AlyssonRowan/MCS-51-Computer/Hardware/(b) Core - HMC-MMB-x Main Memory Board/HMC-MMB-1 Main Memory Board (HY6264A x 4) v1.00 SCHEMATIC .pdf

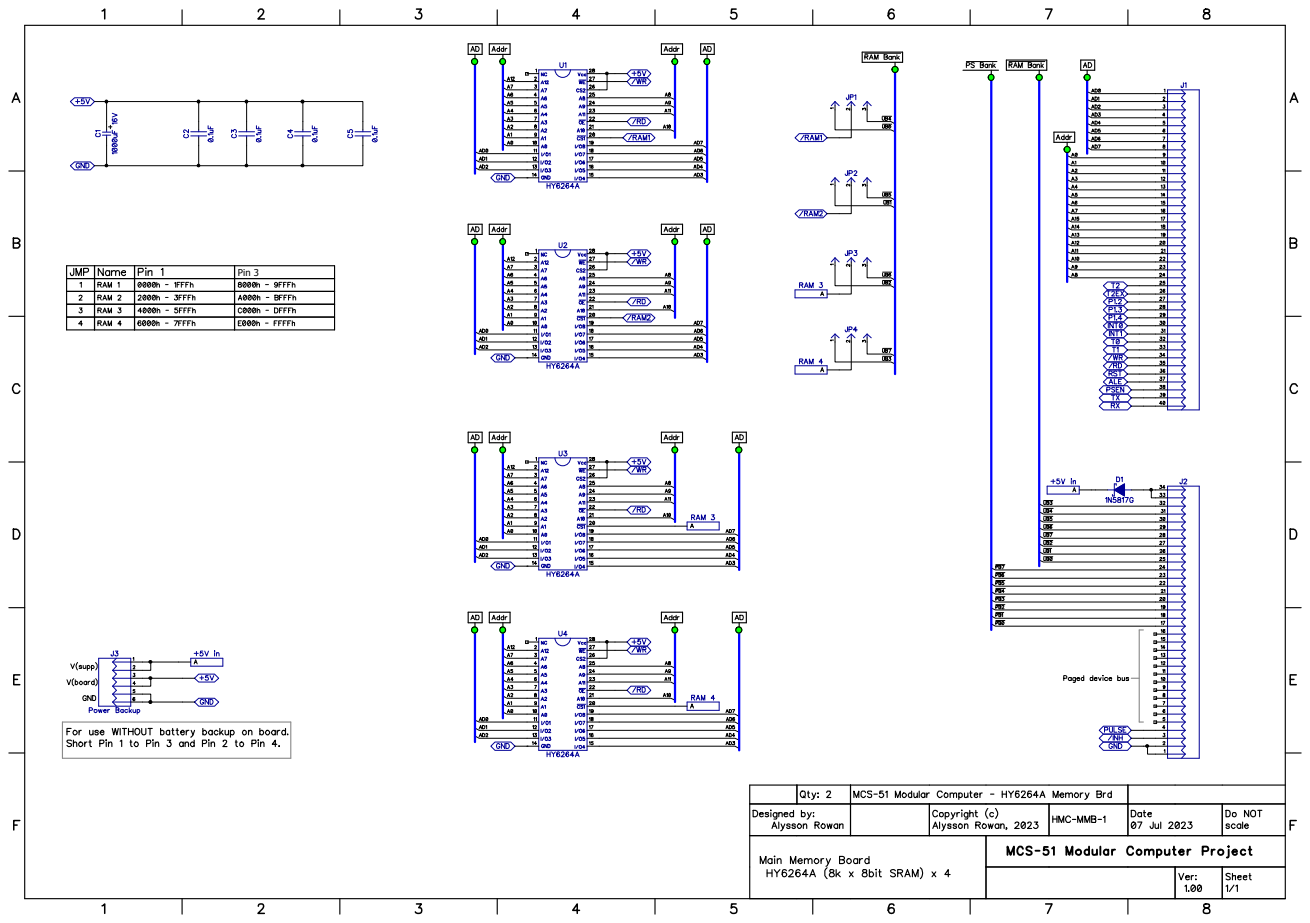
[picture p1: page 1]
Pin 3
