AlyssonRowan/MCS-51-Computer/Hardware/(b) Core - HMC-MMB-x Main Memory Board/HMC-MMB-2 Main Memory Board (configurable W24257AJ) v1.00 SCHEMATIC.pdf

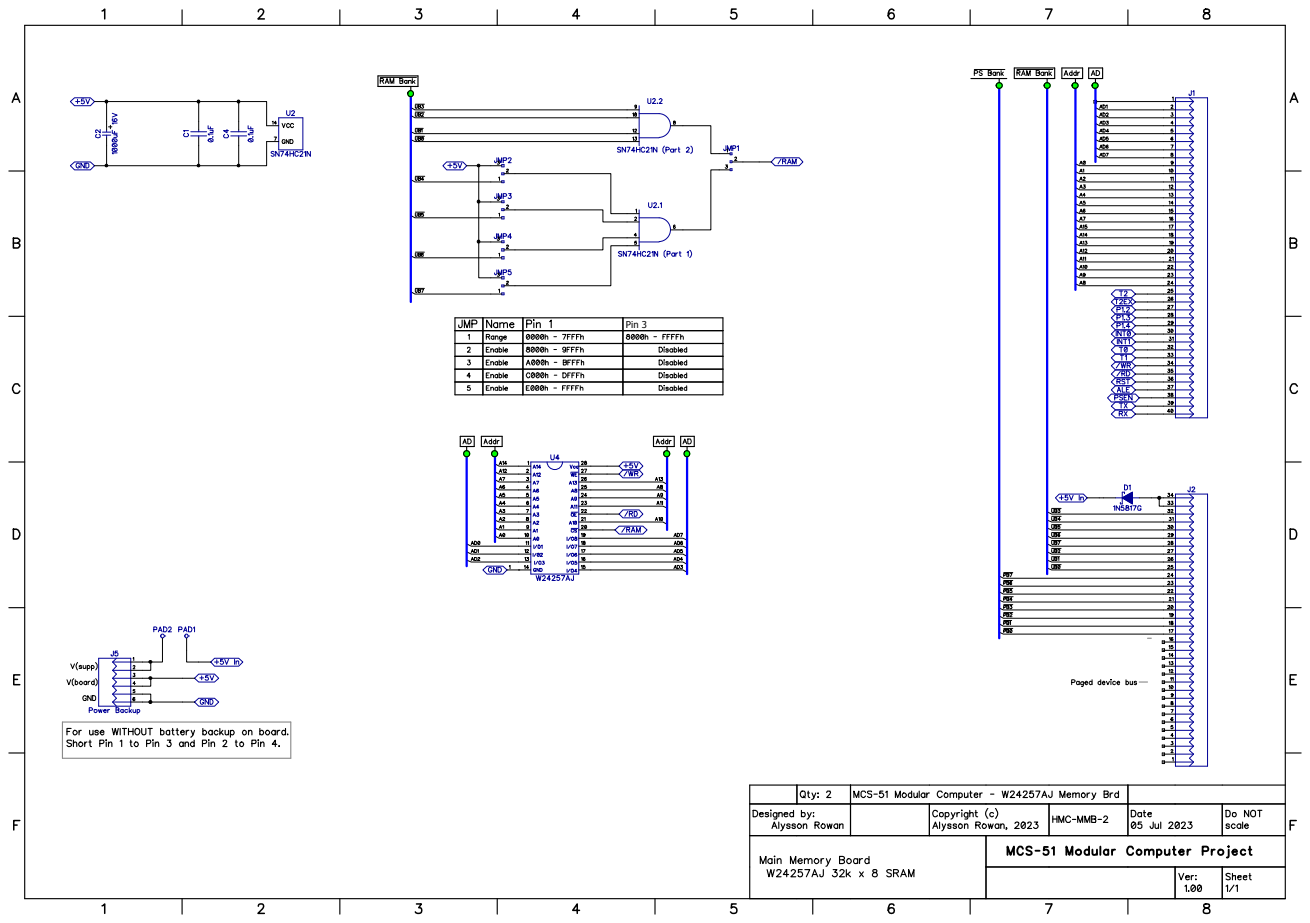
[picture p2: page 1]
Pin 3
