AlyssonRowan/MCS-51-Computer/Hardware/(b) Core - HMC-ROM-x ROM Board/HMC-ROM-1 2764, 128 ROM Board v1.00 SCHEMATIC .pdf

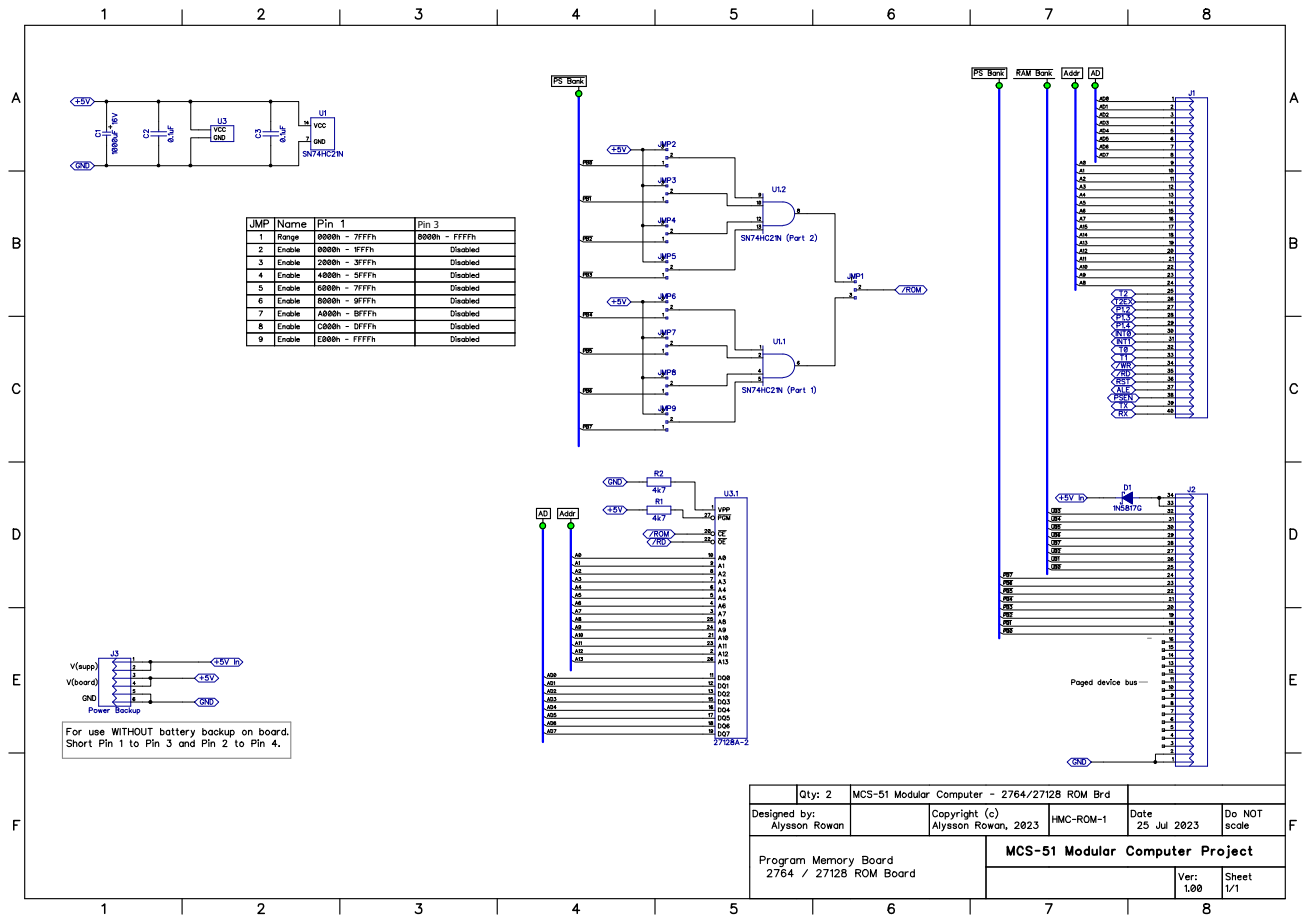
[picture p3: page 1]
Pin 3
