AlyssonRowan/MCS-51-Computer/Hardware/(b) Core - HMC-DCB-x  Daisy-Chain Board/HMC-DCB-2  Daisy-Chain Board (long) v2.00 TOP.pdf

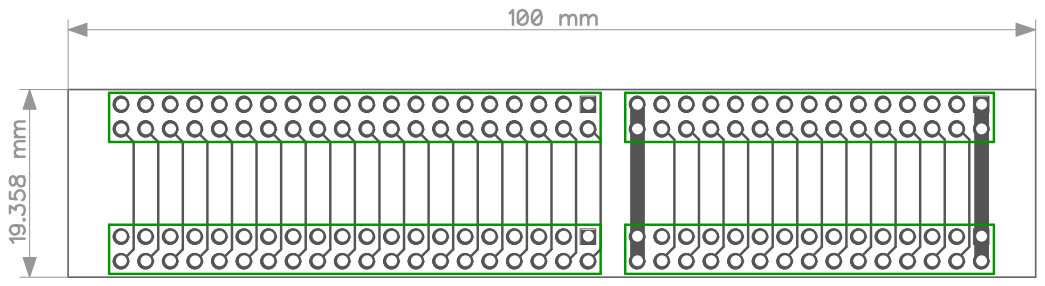
[picture p16: page 1]
