AlyssonRowan/MCS-51-Computer/Hardware/(b) Core - HMC-DCB-x  Daisy-Chain Board/HMC-DCB-2  Daisy-Chain Board (long) v2.00 X-RAY.pdf

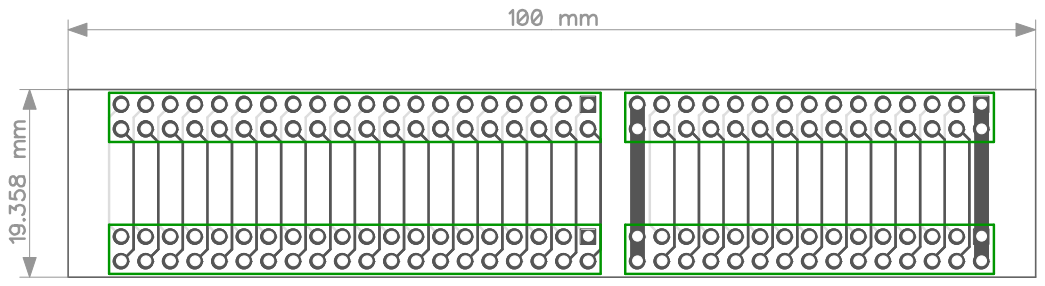
[picture p17: page 1]
