AlyssonRowan/MCS-51-Computer/Hardware/(b) Core - HMC-IB-x  Integrated Backplane/HMC-IB-1  Integrated Backplane MOBO v1.65 BOTTOM.pdf

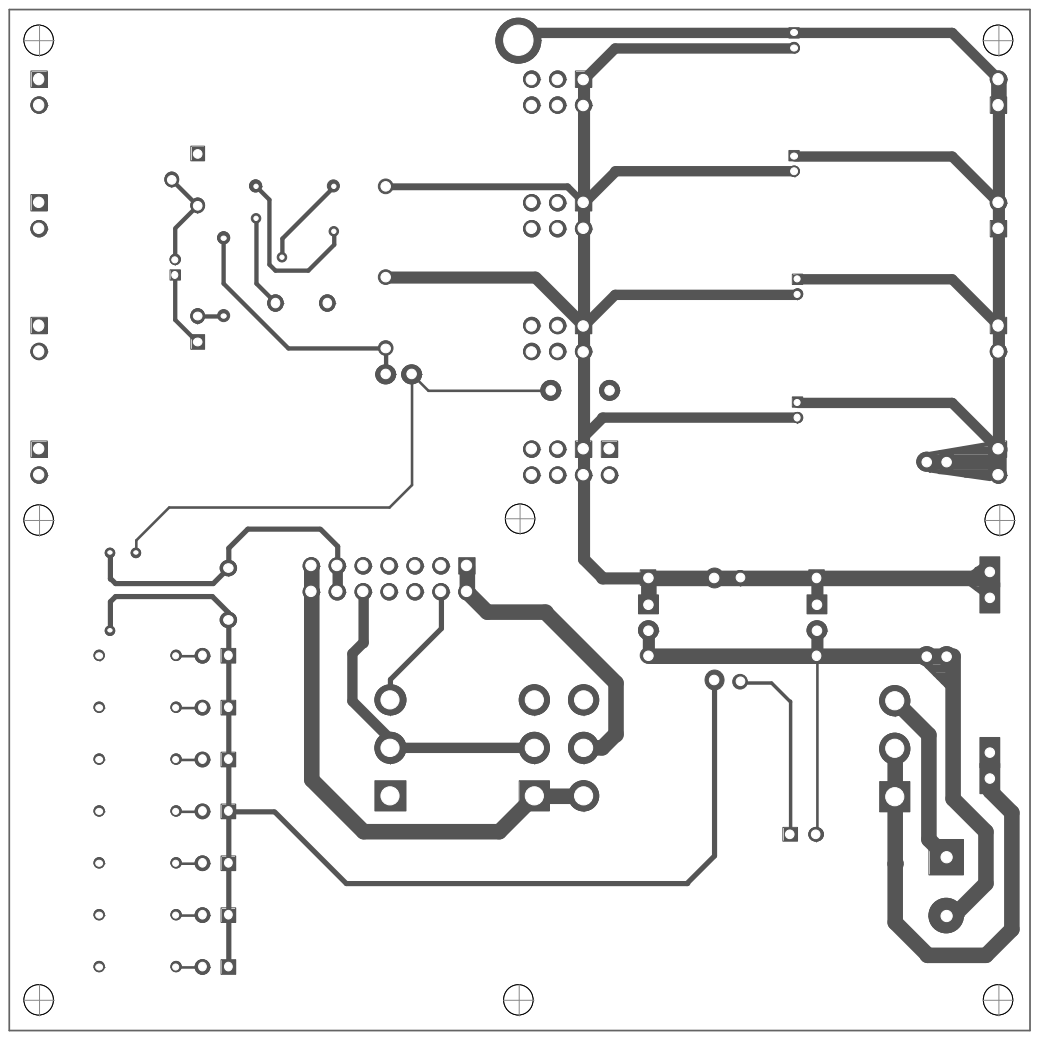
[picture p18: page 1]
