AlyssonRowan/MCS-51-Computer/Hardware/(b) Core - HMC-IB-x  Integrated Backplane/HMC-IB-2  Integrated Backplane BUS daughterboard v1.10 TOP.pdf

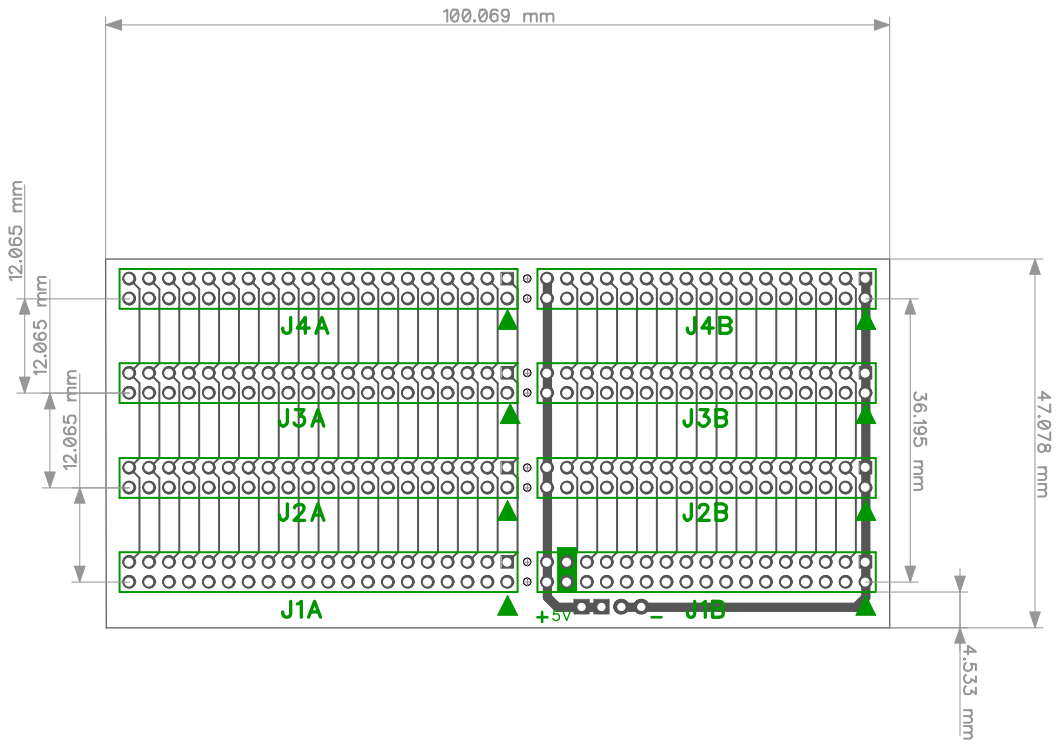
[picture p22: page 1]
