AlyssonRowan/MCS-51-Computer/Hardware/(b) Core - HMC-MB-x  Modular Backplane/HMC-MB-1  Modular Backplane A - 40p v2.00 TOP.pdf

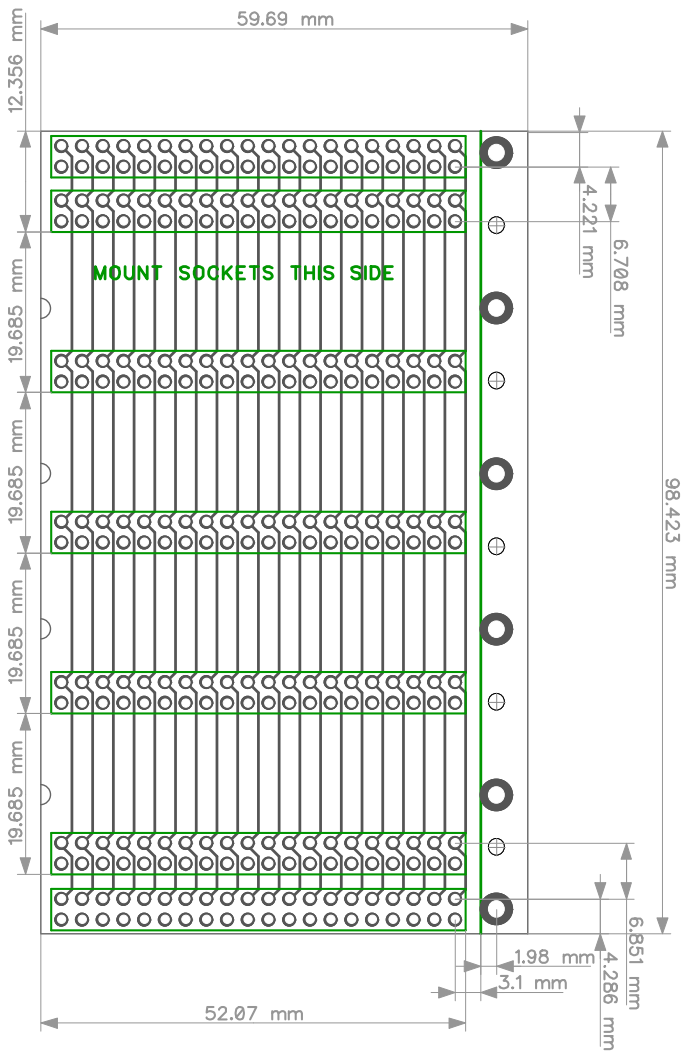
[picture p25: page 1]
