AlyssonRowan/MCS-51-Computer/Hardware/(b) Core - HMC-MB-x  Modular Backplane/HMC-MB-1  Modular Backplane A - 40p v2.00 X-RAY.pdf

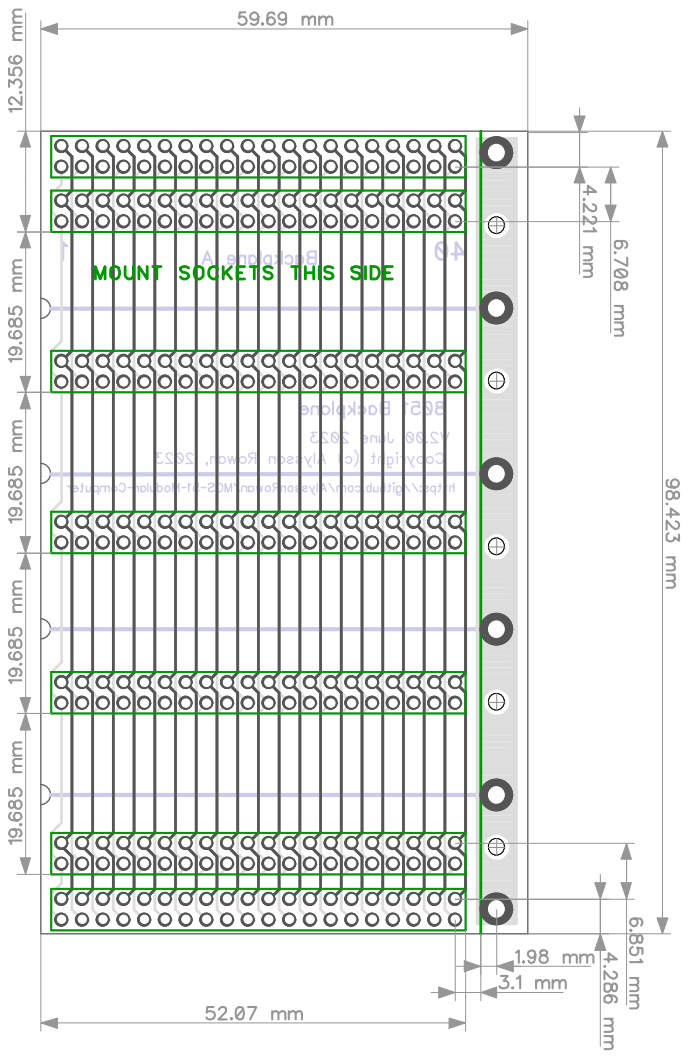
[picture p26: page 1]
