AlyssonRowan/MCS-51-Computer/Hardware/(b) Core - HMC-MB-x  Modular Backplane/HMC-MB-2  Modular Backplane B - 34p v2.00 TOP.pdf

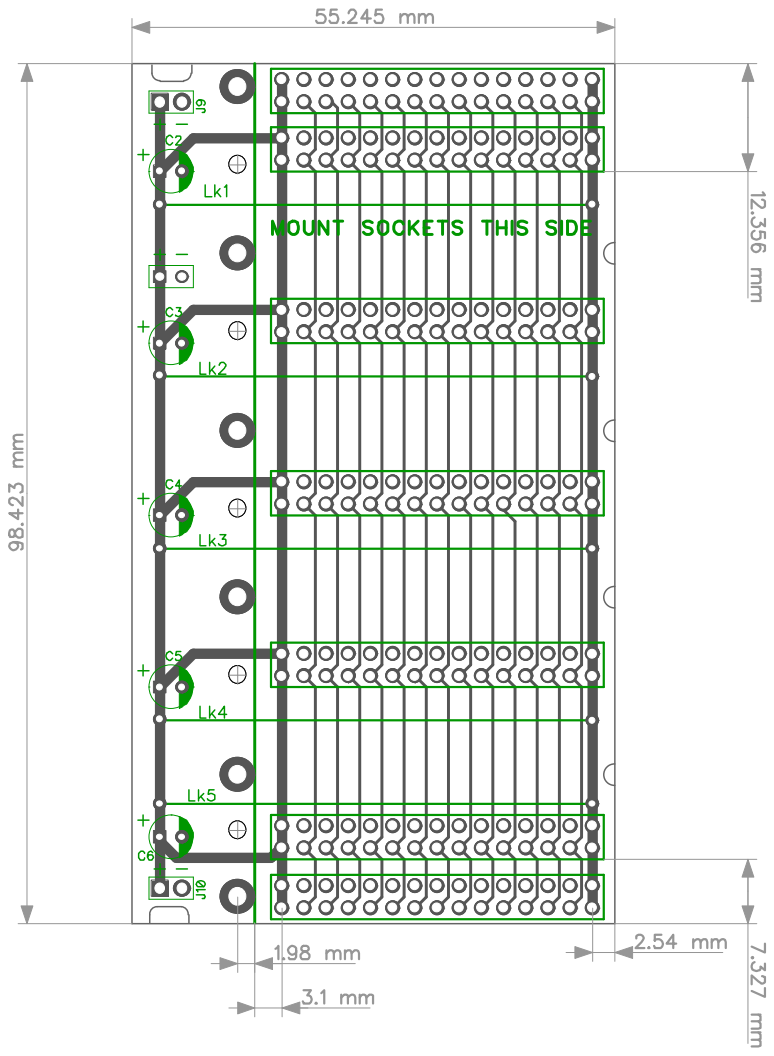
[picture p28: page 1]
