AlyssonRowan/MCS-51-Computer/Hardware/(b) Core - HMC-MB-x  Modular Backplane/HMC-MB-2  Modular Backplane B - 34p v2.00 X-RAY.pdf

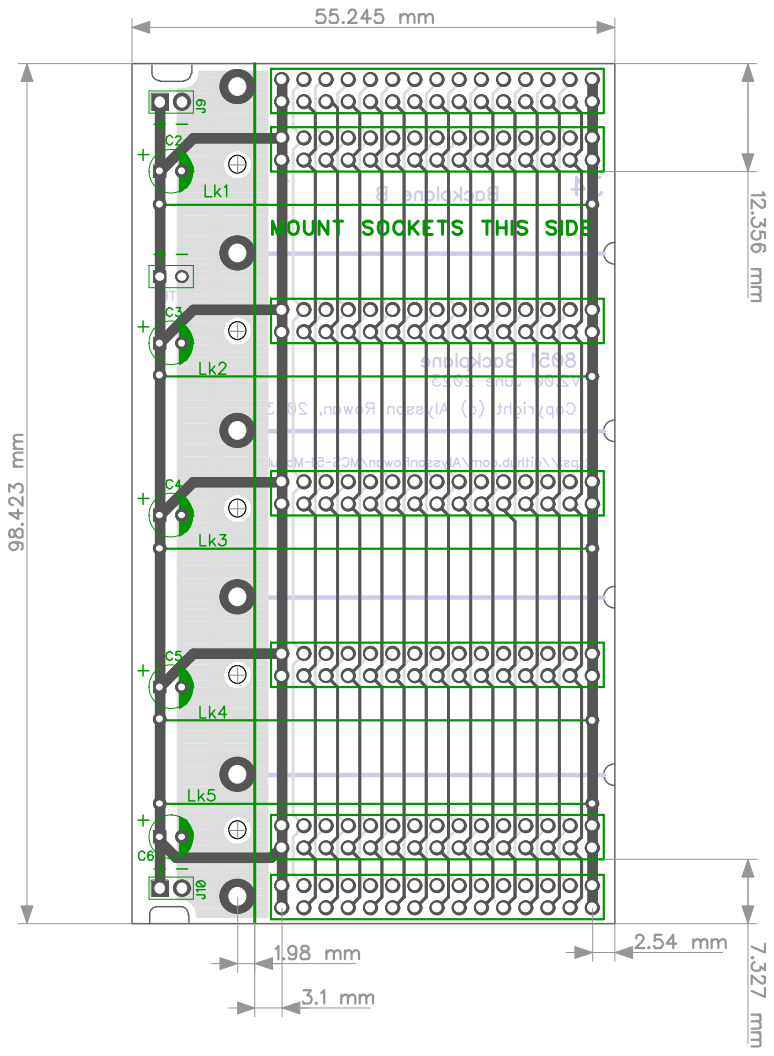
[picture p29: page 1]
