AlyssonRowan/MCS-51-Computer/Hardware/(b) Core - HMC-MMB-x Main Memory Board/HMC-MMB-2 Main Memory Board (configurable W24257AJ) v1.00 BOTTOM.pdf

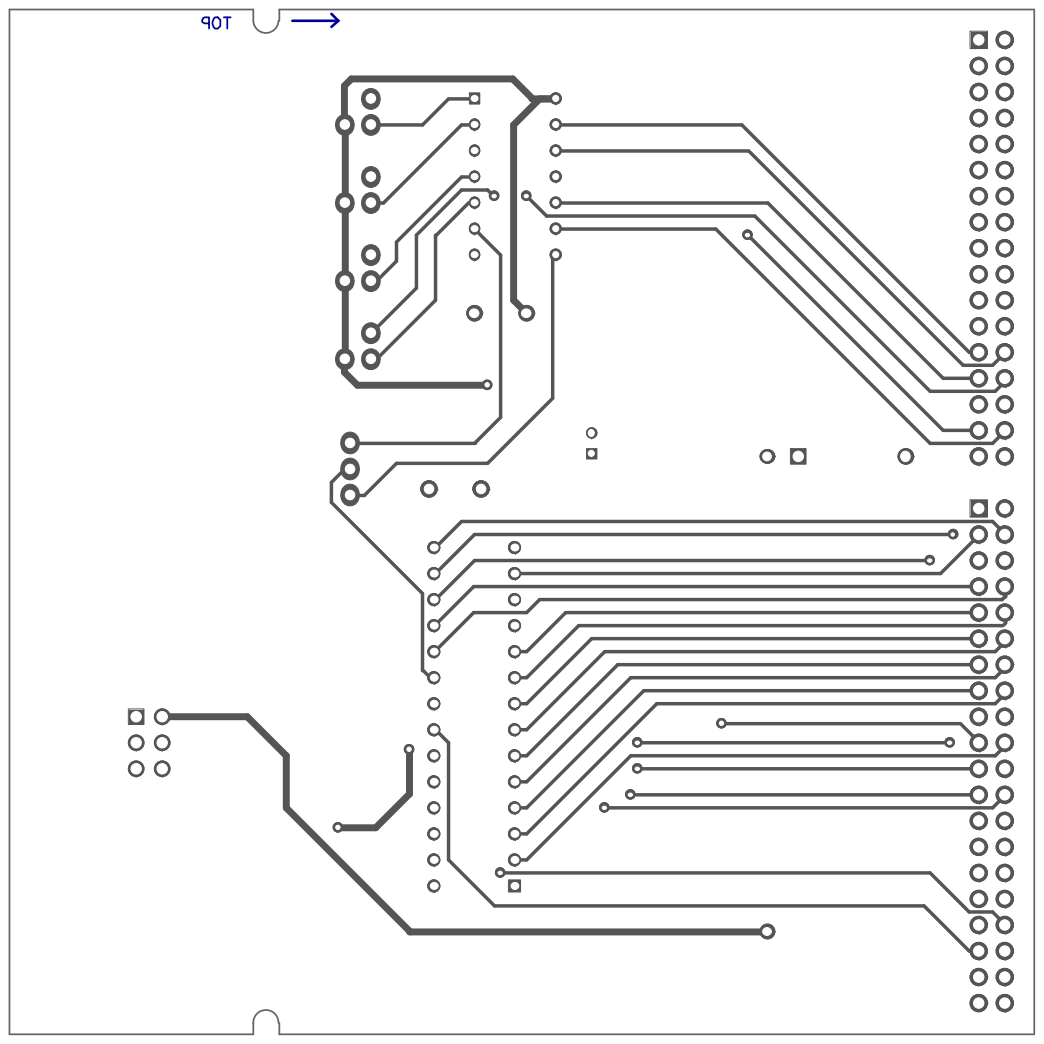
[picture p33: page 1]
