AlyssonRowan/MCS-51-Computer/Hardware/(b) Core - HMC-MMB-x Main Memory Board/HMC-MMB-2 Main Memory Board (configurable W24257AJ) v1.00 TOP.pdf

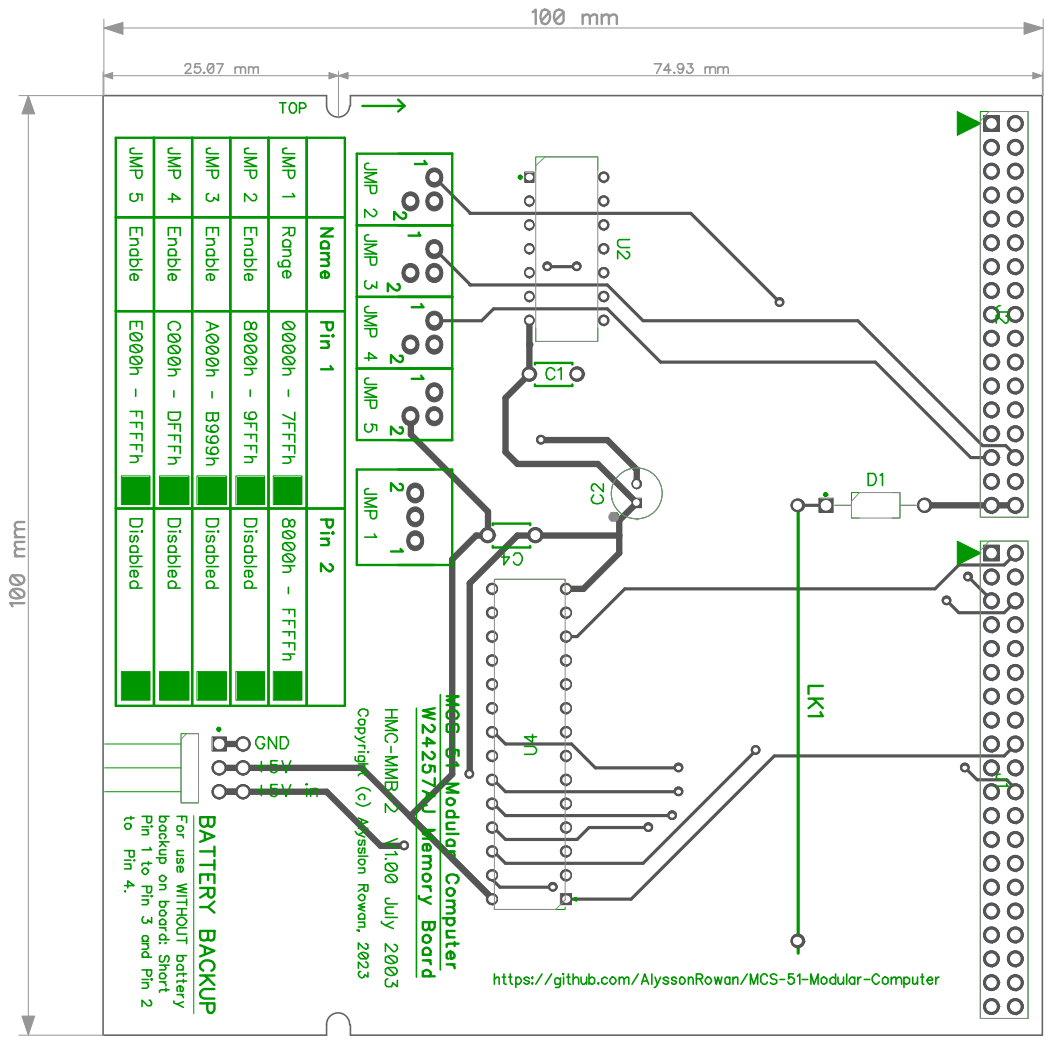
[picture p34: page 1]
