AlyssonRowan/MCS-51-Computer/Hardware/(b) Core - HMC-PB-1  ProductionBackplane/HMC-PB-1 ProductionBackplane (4 slot bus) v1.00 X-RAY.pdf

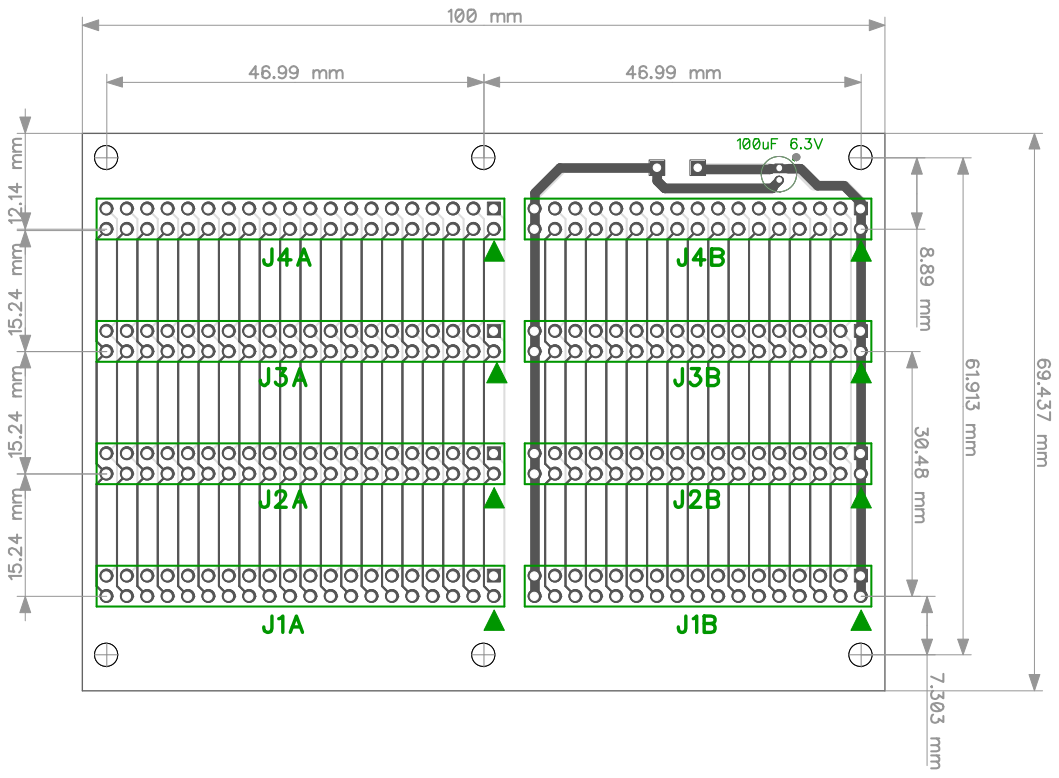
[picture p38: page 1]
