AlyssonRowan/MCS-51-Computer/Hardware/(b) Core - HMC-PR-1 Processor Board/HMC-PR-1 Processor Board v1.20 BOTTOM.pdf

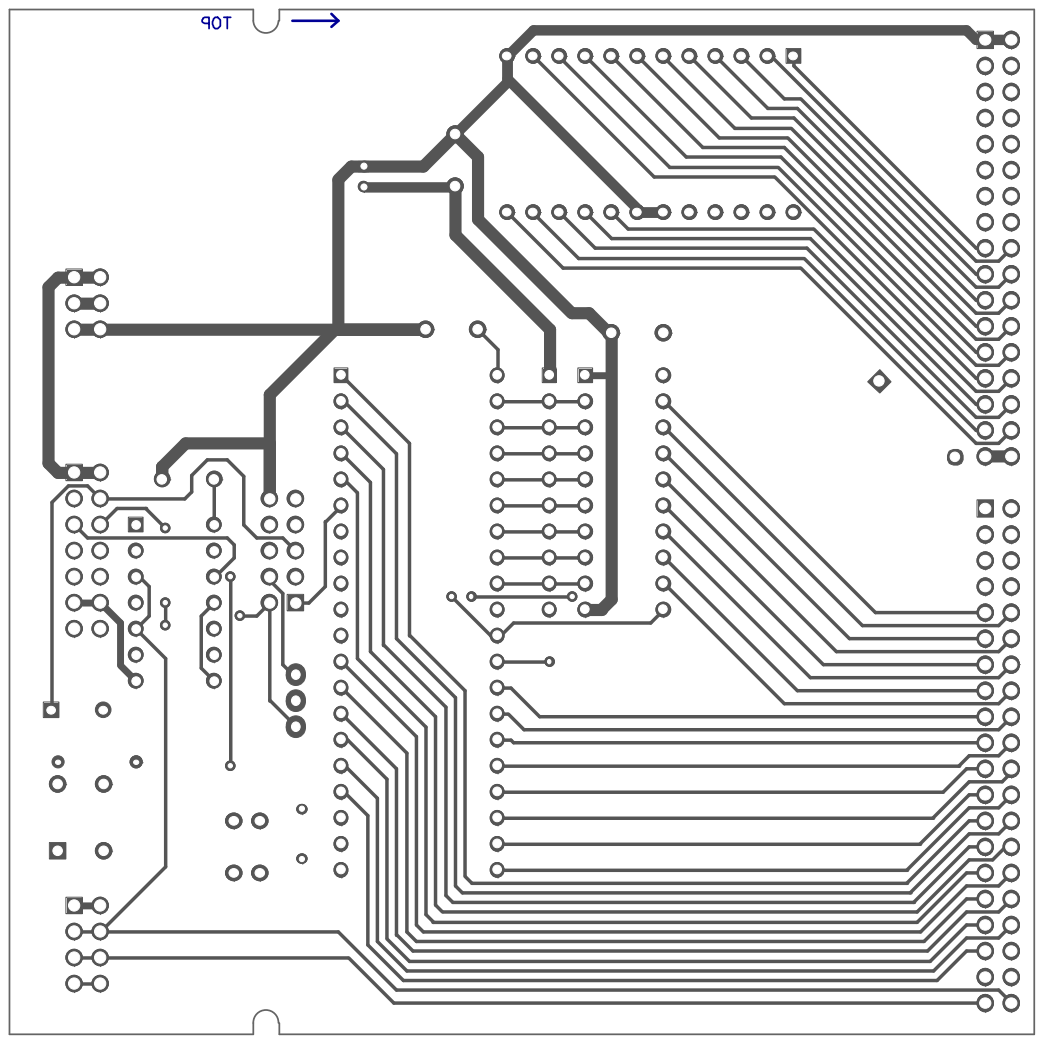
[picture p39: page 1]
