AlyssonRowan/MCS-51-Computer/Hardware/(b) Core - HMC-PR-1 Processor Board/HMC-PR-1 Processor Board v1.20 SCHEMATIC.pdf

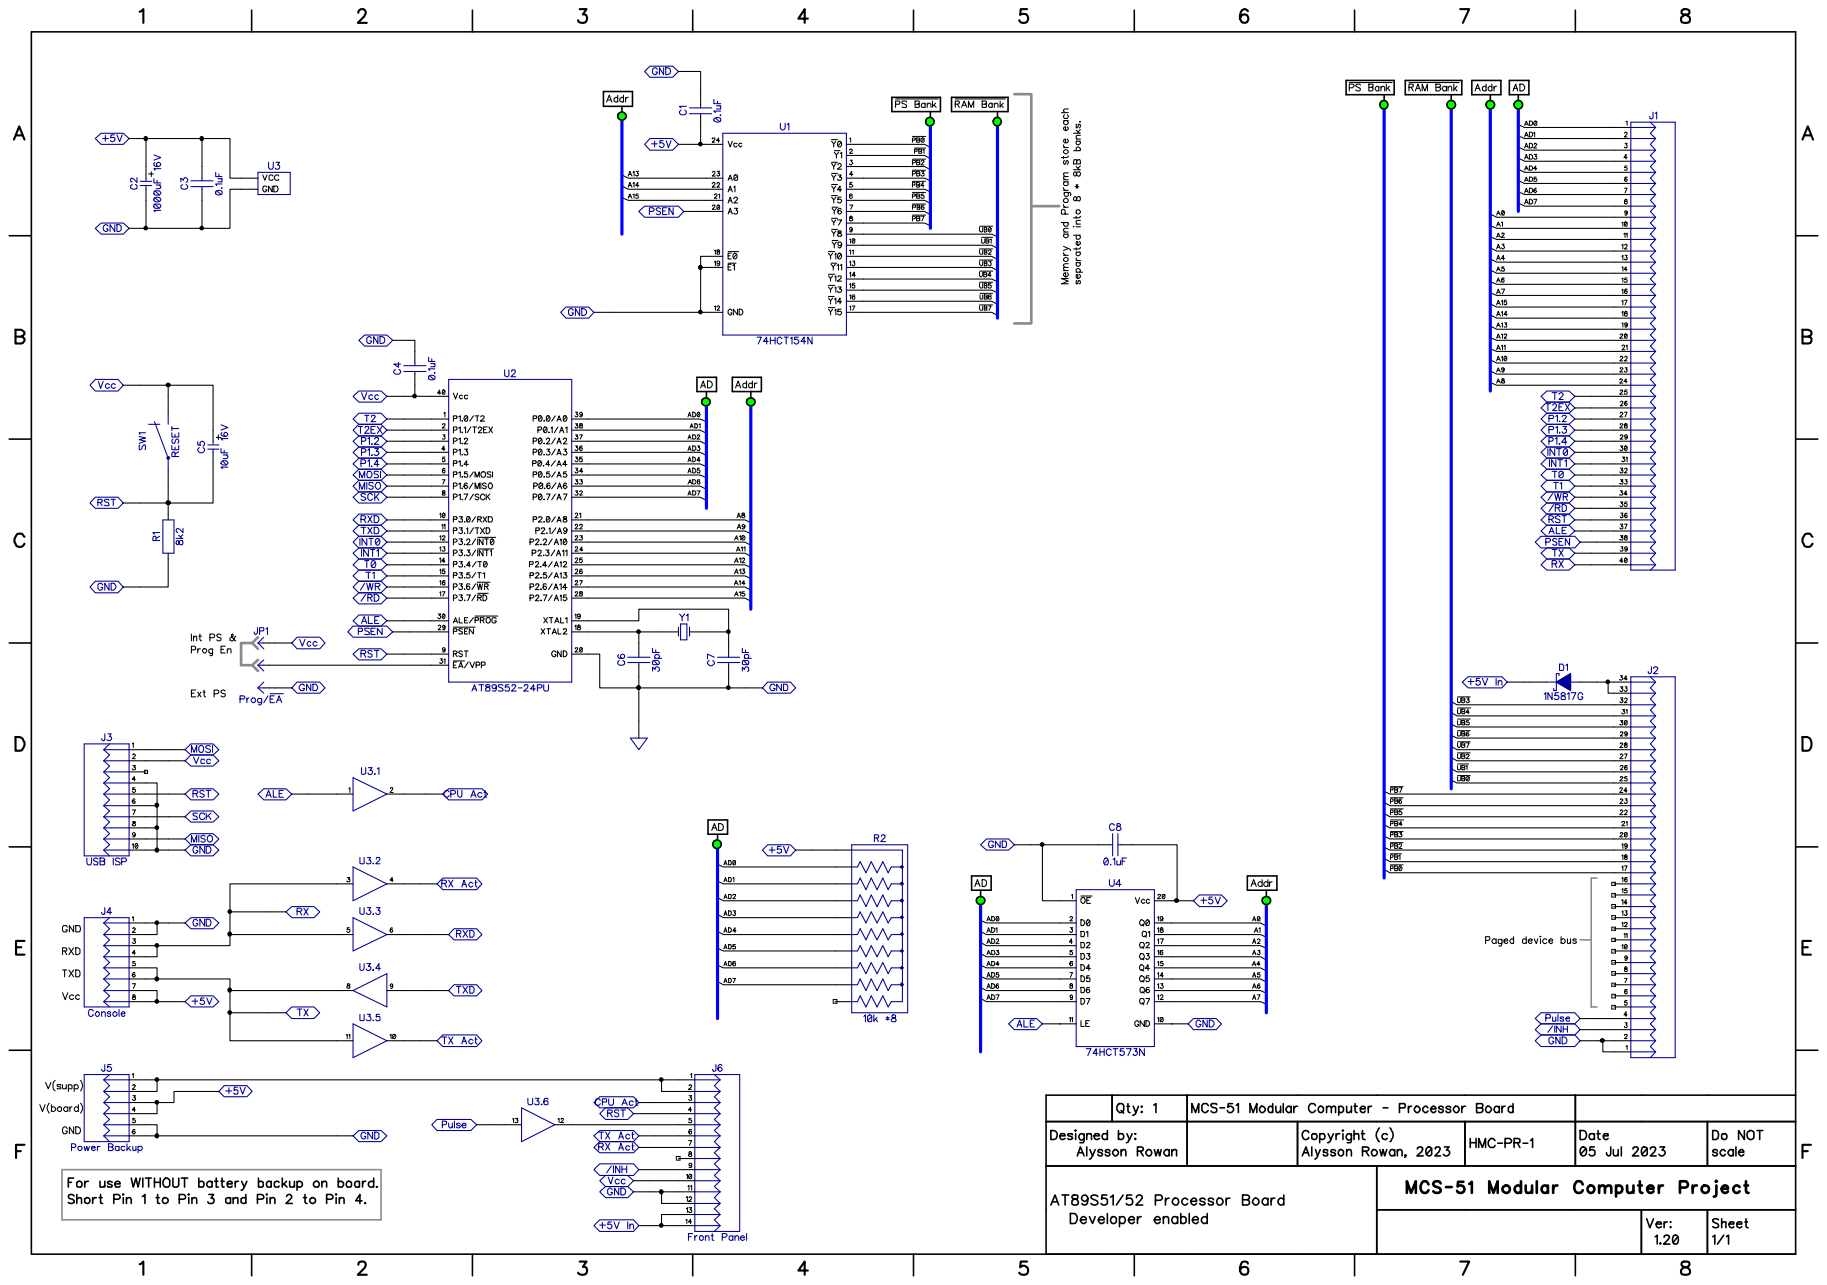
[picture p40: page 1]
