AlyssonRowan/MCS-51-Computer/Hardware/(b) Core - HMC-ROM-x ROM Board/HMC-ROM-1 2764, 128 ROM Board v1.00 TOP .pdf

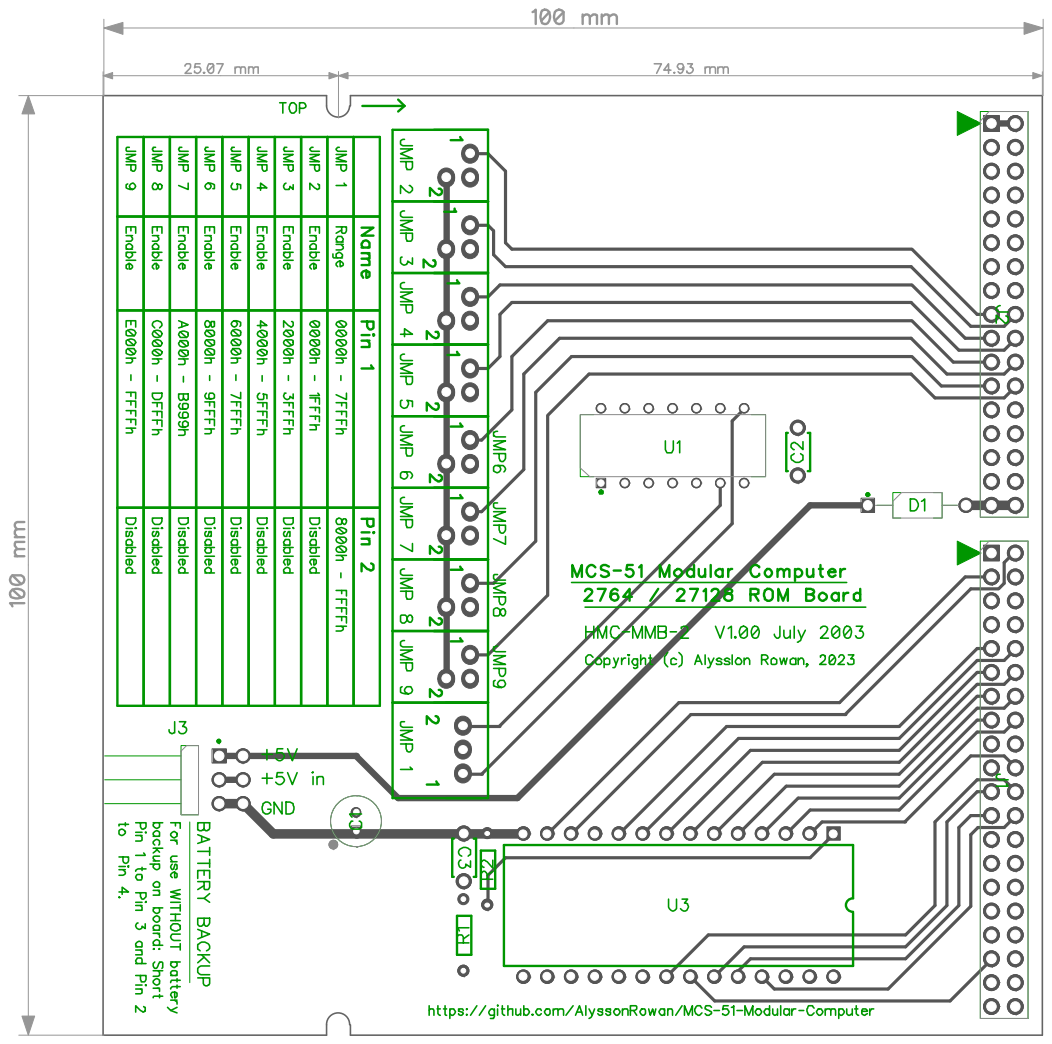
[picture p44: page 1]
