AlyssonRowan/MCS-51-Computer/Hardware/(f) Ancillary - HMC-PB-01 8052AH-BASIC Board Adapter/HMC-PB-01 8052AH-BASIC Board Adaptor V1.00 BOTTOM .pdf

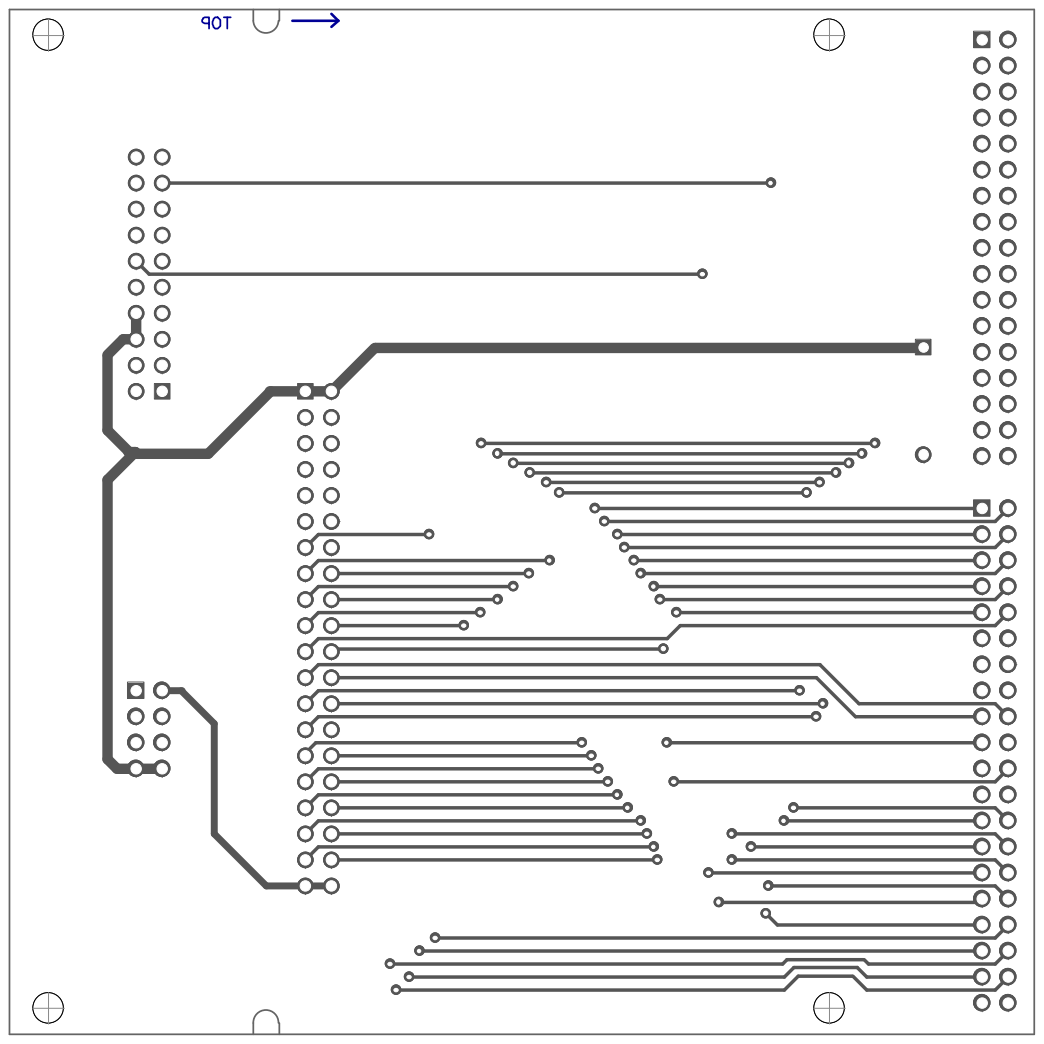
[picture p46: page 1]
