AlyssonRowan/MCS-51-Computer/Hardware/(f) Ancillary - HMC-PB-01 8052AH-BASIC Board Adapter/HMC-PB-01 8052AH-BASIC Board Adaptor V1.00 SCHEMATIC .pdf

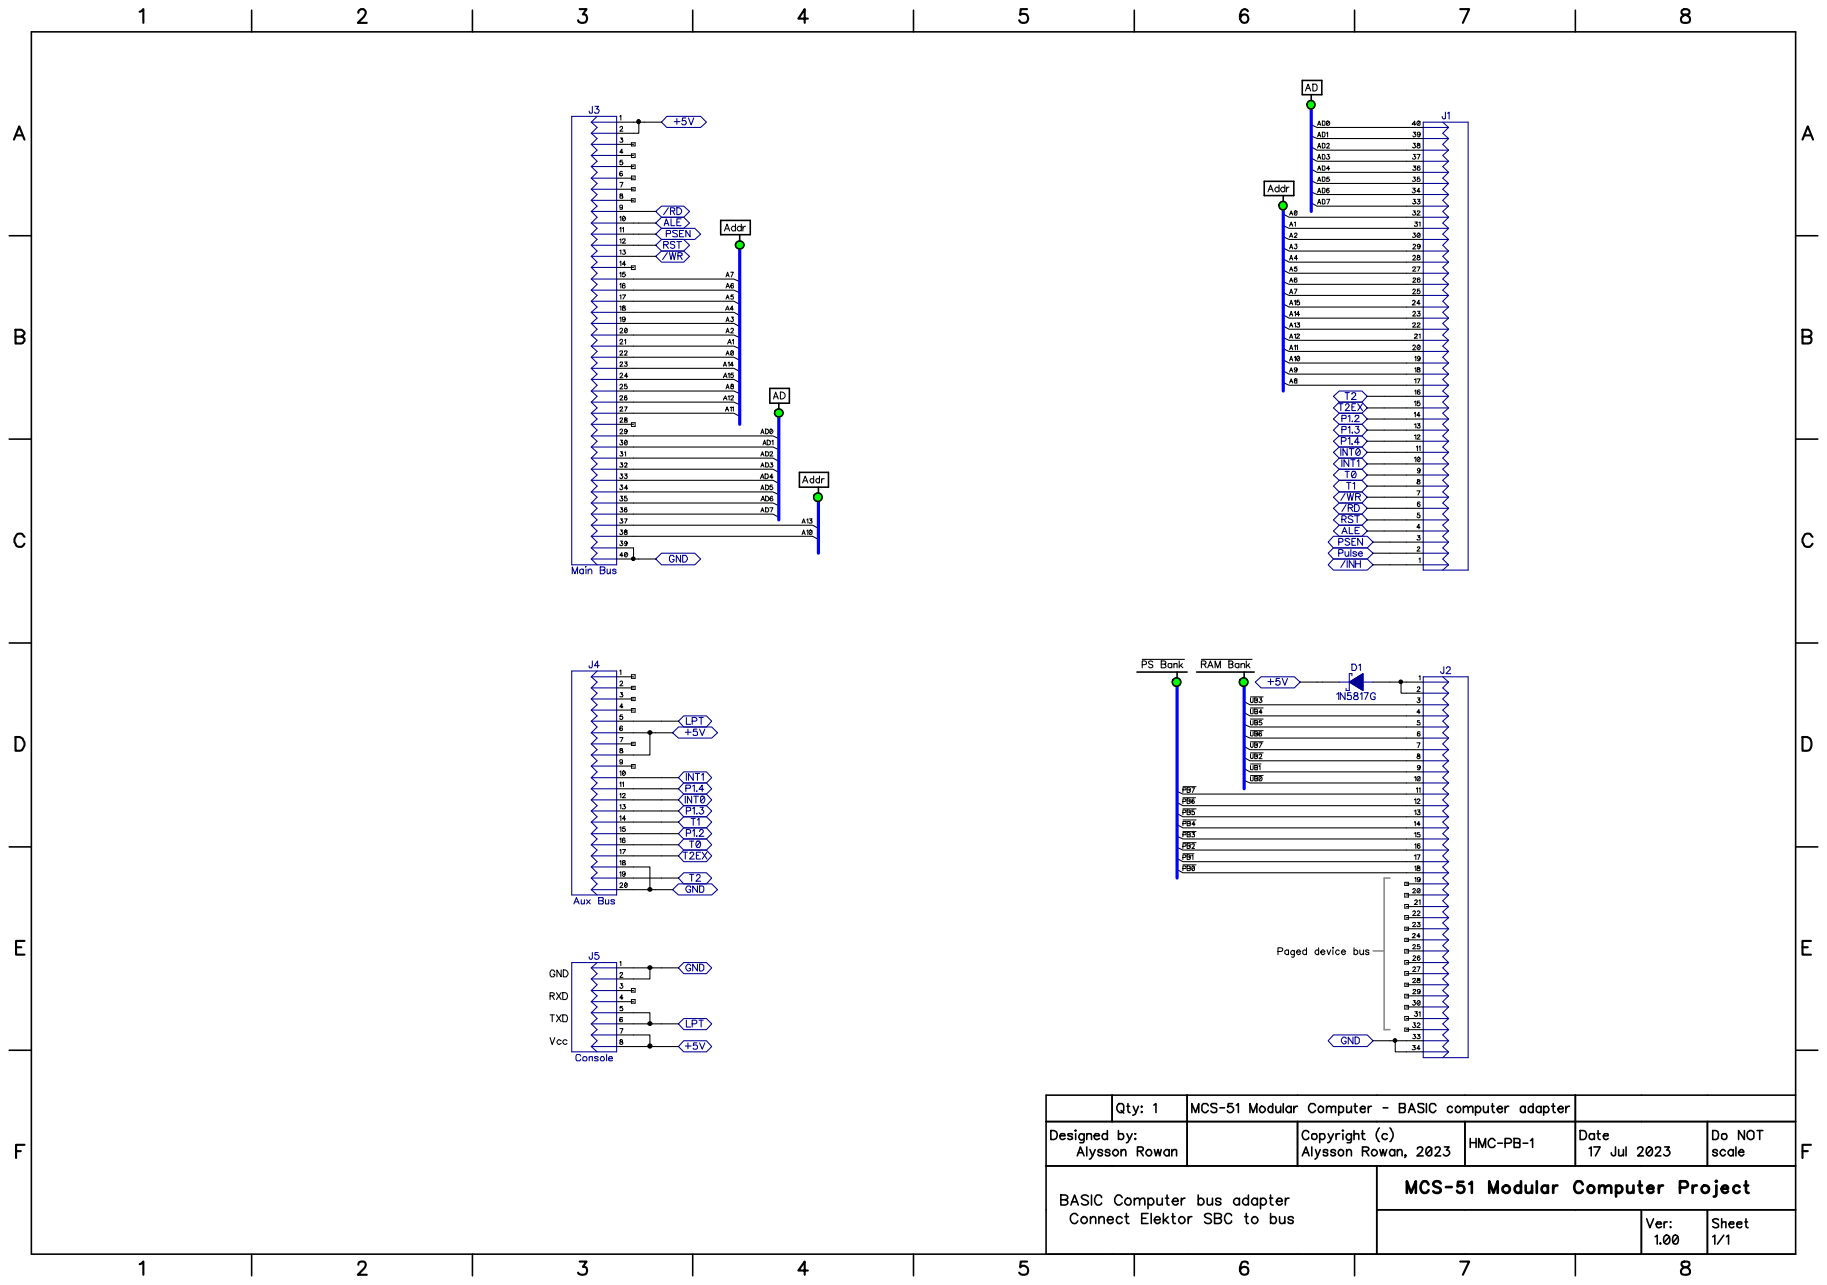
[picture p47: page 1]
